BUNPC/NN22-Technical-Documents/Hardware Peripherial/ninjaNIRS Triggerbox/hardware/Rev2_KiCAD/Docs/Layout_views.pdf

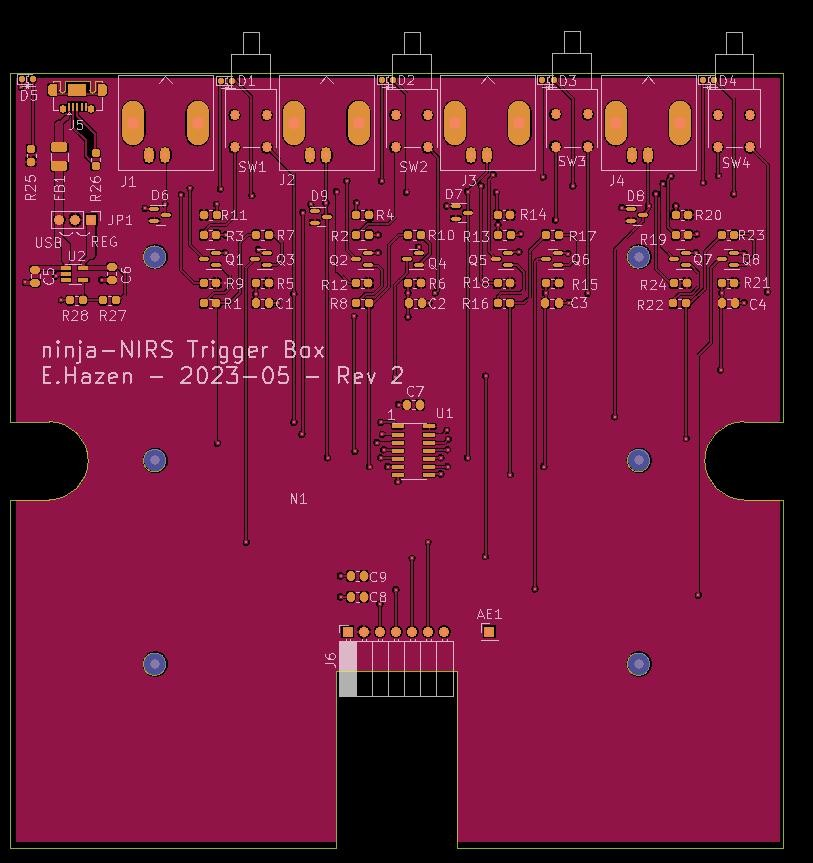
[picture p3: page 1]

Gerber view:
Front Cu, mask, silkscreen. Copper pour is “5V” power

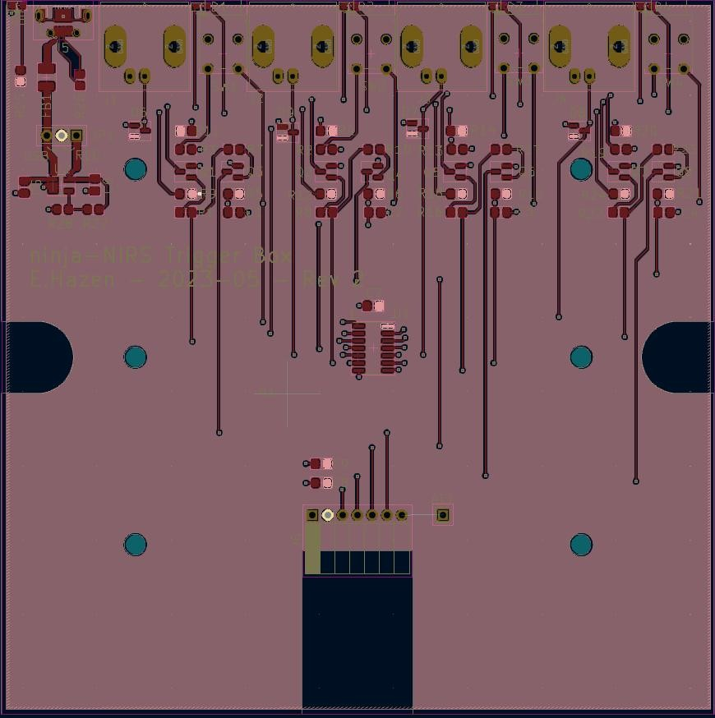
[picture p4: page 2]

5V copper pour with net highlight.

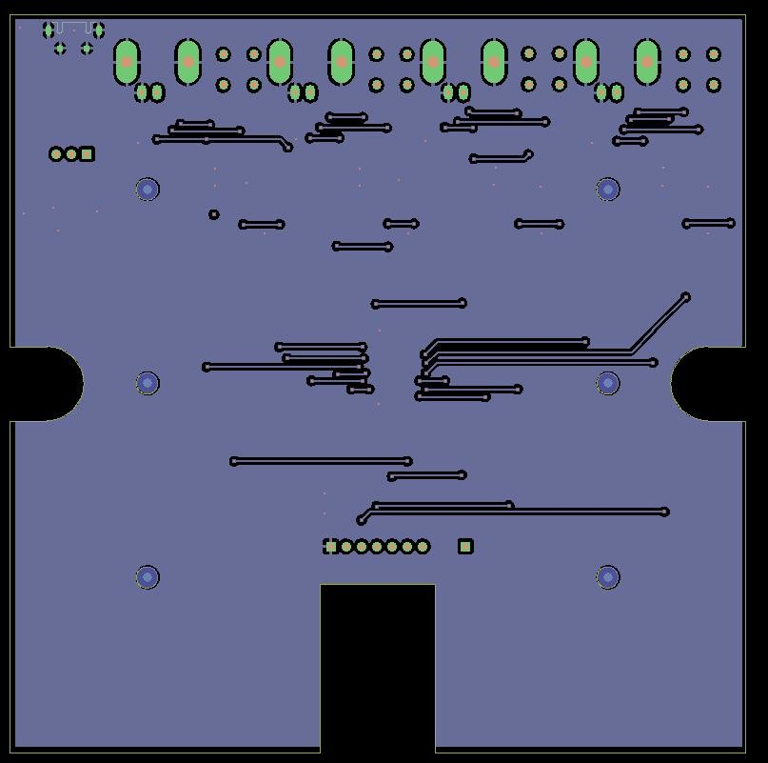
[picture p5: page 3]

Gerber view:
Back Cu, mask.
Copper area is GND

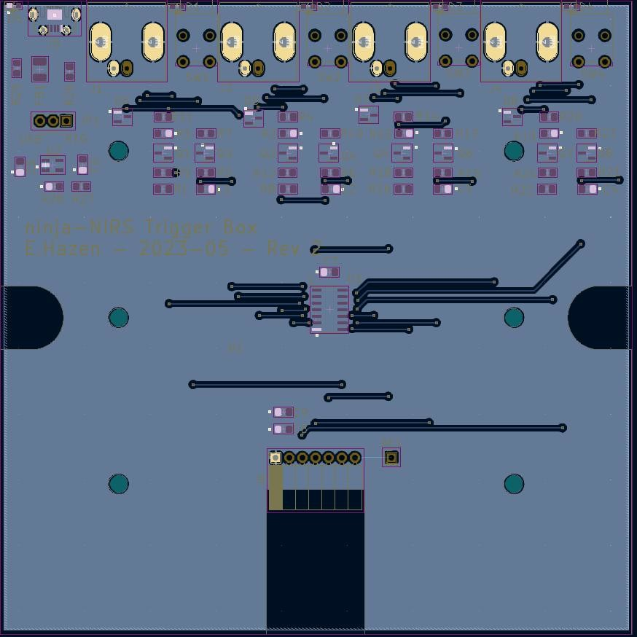
[picture p6: page 4]

Copper pour with GND highlighted

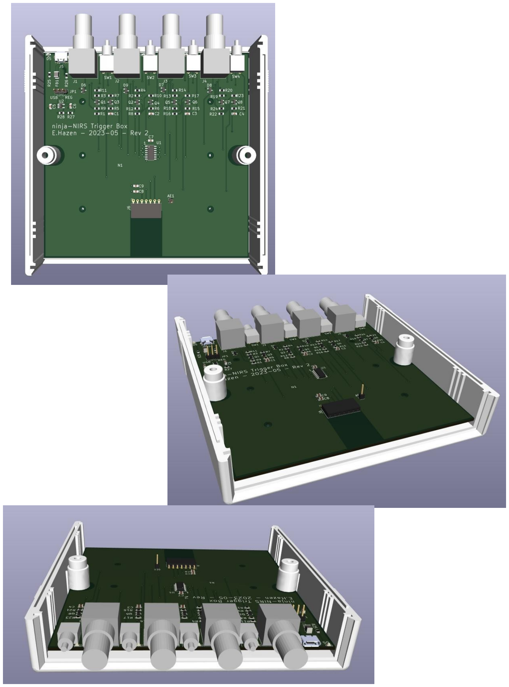
[picture p7: page 5]
