BUNPC/NN22-Technical-Documents/Hardware Main/Electronics/Source Electronics/SRC_InterfaceCard/NN22_7Lvl_ResSrcAdapter02_s00.XYRS.csv

#XYRS data for NN22_7Lvl_ResSrcAdapter02_s00.brd.
#Board Size is 2500.000000 x 1300.000000.
#
#Placement Data:
#Designator | X-Loc | Y-Loc | Rotation | Side | Type | X-Size | Y-Size | Value | Footprint | Populate | MPN
C1 | 1690.00 | 1135.00 | 180 | 1 | 1 | 340.55 | 98.43 | 100u | 2917-CAP | 1
C2 | 1960.00 | 880.00 | 270 | 1 | 1 | 169.29 | 70.87 | 22u | 1206 | 1
C3 | 2070.00 | 880.00 | 270 | 1 | 1 | 169.29 | 70.87 | 22u | 1206 | 1
C4 | 1840.00 | 790.00 | 180 | 1 | 1 | 62.99 | 19.69 | 0.1u | 0402-CAP | 1
C5 | 1675.00 | 870.00 | 270 | 1 | 1 | 62.99 | 19.69 | 47p | 0402-CAP | 1
C6 | 1600.00 | 970.00 | 180 | 1 | 1 | 169.29 | 70.87 | 22u | 1206 | 1
C7 | 1350.00 | 990.00 | 0 | 1 | 1 | 62.99 | 19.69 | 0.1u | 0402-CAP | 1
C8 | 1320.00 | 475.00 | 270 | 1 | 1 | 62.99 | 19.69 | 0.1u | 0402-CAP | 1
C9 | 1260.00 | 475.00 | 270 | 1 | 1 | 62.99 | 19.69 | 0.1u | 0402-CAP | 1
C10 | 1240.00 | 190.00 | 270 | 1 | 1 | 169.29 | 70.87 | 22u | 1206 | 1
C11 | 1240.00 | 1110.00 | 90 | 1 | 1 | 169.29 | 70.87 | 22u | 1206 | 1
D1 | 170.00 | 950.00 | 0 | 2 | 1 | 78.74 | 27.56 | SBR1A20T5 | SOD523 | 1
D2 | 335.00 | 850.00 | 0 | 2 | 1 | 78.74 | 27.56 | SBR1A20T5 | SOD523 | 1
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
