BUNPC/NN22-Technical-Documents/Hardware Peripherial/ninjaNIRS Triggerbox/hardware/Rev1a_Eagle/81kcTXVxWdL._AC_SL1500_.jpg

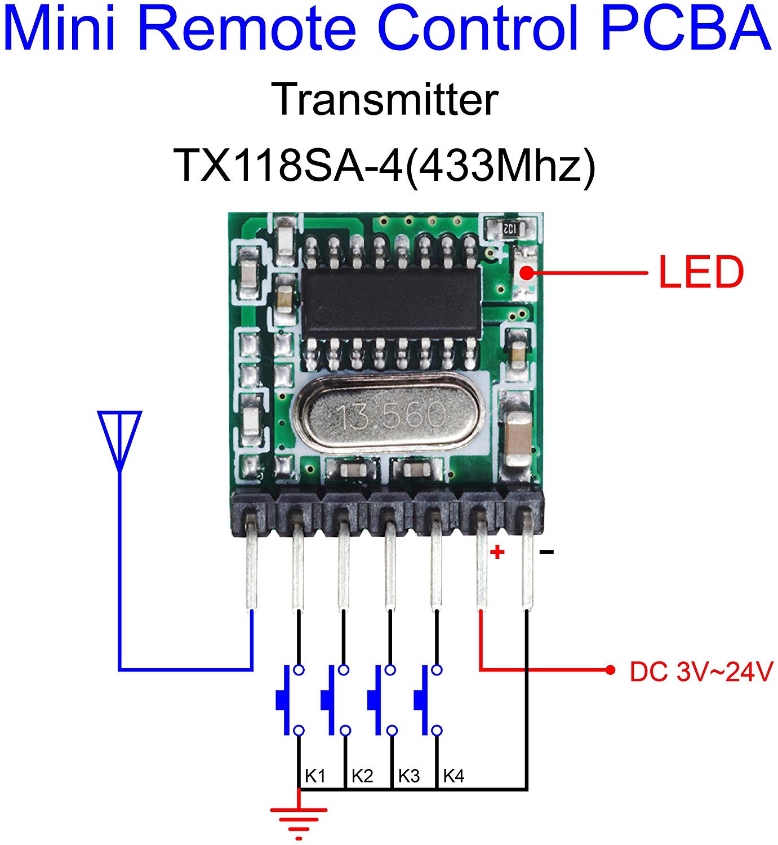
Hardware Peripherial/ninjaNIRS Triggerbox/hardware/Rev1a_Eagle/81kcTXVxWdL._AC_SL1500_.jpg
