BUNPC/NN22-Technical-Documents/Hardware Main/Electronics/Detector Electronics/Det_InterfaceCard/NN22_RPi_DetAdapter02_s00_BOM.xlsx

Designator | Value | Footprint | Populate | MPN | Manufacturer
C1 | 330p | 0402-CAP | 1 | GRM1555C1H331JA01D | Murata
C10 | 0.1u | 0402-CAP | 1 | GRM155R71H104KE14D | Murata
C100 | 0.1u | 0402-CAP | 1 | GRM155R71H104KE14D | Murata
C101 | 0.1u | 0402-CAP | 1 | GRM155R71H104KE14D | Murata
C102 | 0.1u | 0402-CAP | 1 | GRM155R71H104KE14D | Murata
C103 | 0.1u | 0402-CAP | 1 | GRM155R71H104KE14D | Murata
C104 | 10u | 0603-CAP | 1 | GRM188R6YA106MA73D | Murata
C105 | 4.7u | 0402-CAP | 1 | CL05A475MP5NRNC | Samsung
C106 | 10u | 0603-CAP | 1 | GRM188R6YA106MA73D | Murata
C107 | 4.7u | 0402-CAP | 1 | CL05A475MP5NRNC | Samsung
C108 | 10u | 0603-CAP | 1 | GRM188R6YA106MA73D | Murata
C109 | 10u | 0603-CAP | 1 | GRM188R6YA106MA73D | Murata
C11 | 330p | 0402-CAP | 1 | GRM1555C1H331JA01D | Murata
C110 | 33n | 0402-CAP | 1 | GCM155R71E333KA55D | Murata
C111 | 4.7u | 0402-CAP | 1 | CL05A475MP5NRNC | Samsung
C112 | 4.7u | 0402-CAP | 1 | CL05A475MP5NRNC | Samsung
C113 | 4.7u | 0402-CAP | 1 | CL05A475MP5NRNC | Samsung
C12 | 1u | 0402-CAP | 1 | CL05A105KP5NNNC | Samsung
C13 | 0.1u | 0402-CAP | 1 | GRM155R71H104KE14D | Murata
C14 | 1u | 0402-CAP | 1 | CL05A105KP5NNNC | Samsung
C15 | 1n | 0402-CAP | 1 | GRM1555C1H102JA01D | Murata
C16 | 1n | 0402-CAP | 1 | GRM1555C1H102JA01D | Murata
C17 | 1n | 0402-CAP | 1 | GRM1555C1H102JA01D | Murata
C18 | 330p | 0402-CAP | 1 | GRM1555C1H331JA01D | Murata
C19 | 0.1u | 0402-CAP | 1 | GRM155R71H104KE14D | Murata
C2 | 1n | 0402-CAP | 1 | GRM1555C1H102JA01D | Murata
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
TP8 | TESTPOINT_ROUND | TESTPAD_ROUND | 0
TP9 | TESTPOINT_ROUND | TESTPAD_ROUND | 0
U1 | AD7380 | LFCSP16 | 1 | AD7380BCPZ-RL7 | Analog Devices
U10 | RP2040 | QFN-56_EP | 1 | SC0914(7) | Raspberry Pi
U11 | MCP1755_DFN | DFN8_2X3MM | 1 | MCP1755-3302E/MC | Microchip
U12 | MCP1755_DFN | DFN8_2X3MM | 1 | MCP1755-3302E/MC | Microchip
U13 | ADP7142_WSON | WSON6 | 1 | ADP7142ACPZN5.0-R7 | Analog Devices
U14 | ADP7182_WSON | WSON6 | 1 | ADP7182ACPZN-R7 | Analog Devices
U15 | ADP7182_WSON | WSON6 | 1 | ADP7182ACPZN-R7 | Analog Devices
U2 | ADA4940-2 | LFCSP24 | 1 | ADA4940-2ACPZ-R7 | Analog Devices
U3 | AD7380 | LFCSP16 | 1 | AD7380BCPZ-RL7 | Analog Devices
U4 | ADA4940-2 | LFCSP24 | 1 | ADA4940-2ACPZ-R7 | Analog Devices
U5 | AD7380 | LFCSP16 | 1 | AD7380BCPZ-RL7 | Analog Devices
U6 | ADA4940-2 | LFCSP24 | 1 | ADA4940-2ACPZ-R7 | Analog Devices
U7 | AD7380 | LFCSP16 | 1 | AD7380BCPZ-RL7 | Analog Devices
U8 | ADA4940-2 | LFCSP24 | 1 | ADA4940-2ACPZ-R7 | Analog Devices
U9 | W25Q_USON | USON8L-2X3MM | 1 | W25Q16JVUXIQ TR | Winbond
X1 | CRYSTAL-3.2-2.5 | CRYSTAL-3.2-2.5 | 1 | 403I35D12M00000 | CTS Components
