BUNPC/NN22-Technical-Documents/Hardware Peripherial/ninjaNIRS Triggerbox/hardware/Rev2_KiCAD/3D/1598B Top.stp

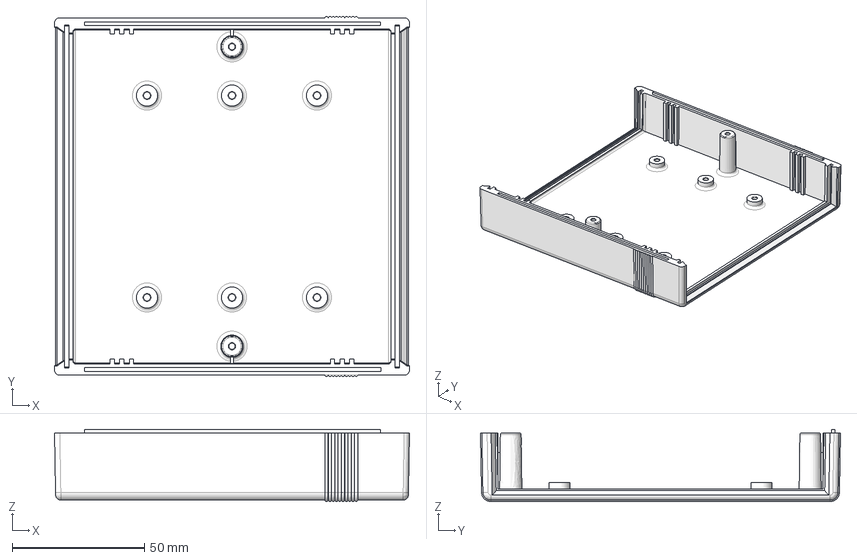
[picture p27: CAD file, 2024-05-28]
Hardware Peripherial/ninjaNIRS Triggerbox/hardware/Rev2_KiCAD/3D/1598B Top.stp
134.3 x 136.2 x 27.2 mm
