BUNPC/NN22-Technical-Documents/Hardware Peripherial/ninjaNIRS Triggerbox/hardware/Rev2_KiCAD/panel/panel.dxf

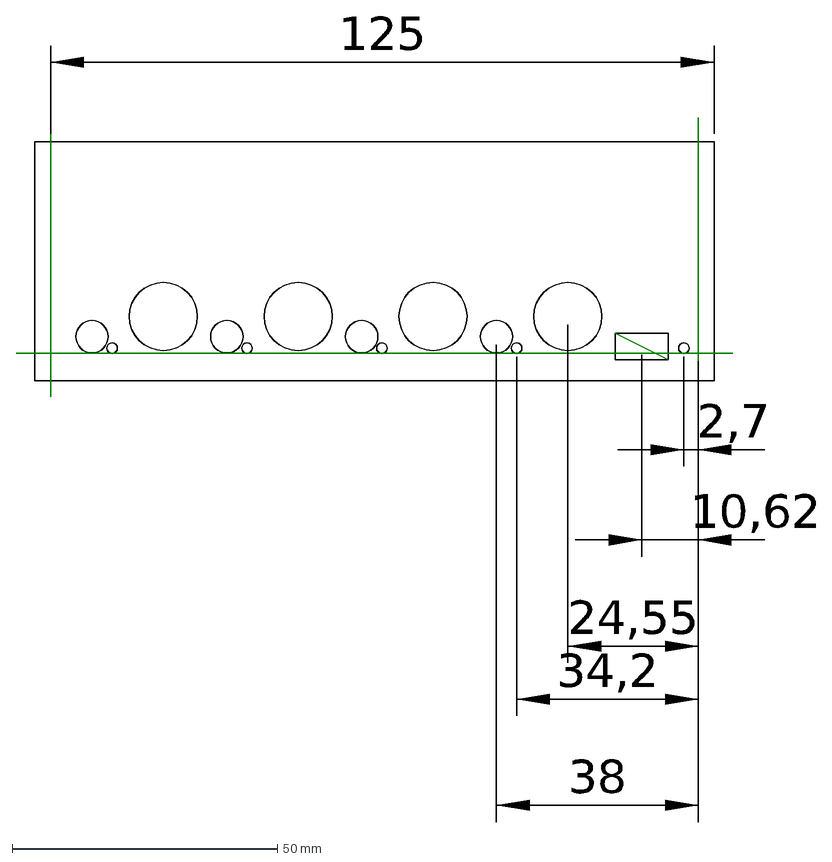
[picture p28: CAD file, 2024-05-28]
Hardware Peripherial/ninjaNIRS Triggerbox/hardware/Rev2_KiCAD/panel/panel.dxf
125
2,7
10,62
24,55
34,2
38
