BUNPC/NN22-Technical-Documents/Hardware Peripherial/ninjaNIRS Triggerbox/hardware/Rev2_KiCAD/trigger-board/Hammond_1598B.dxf

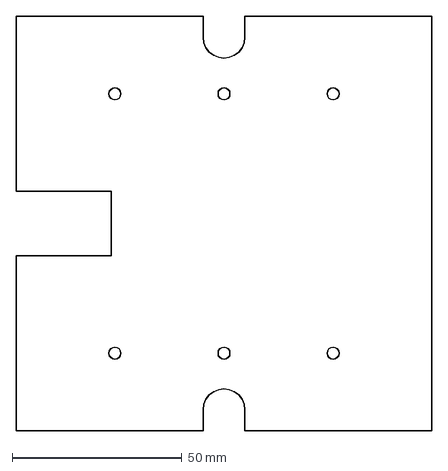
[picture p29: CAD file, 2024-05-28]
Hardware Peripherial/ninjaNIRS Triggerbox/hardware/Rev2_KiCAD/trigger-board/Hammond_1598B.dxf
122.3 x 122.0 mm
