BUNPC/NN22-Technical-Documents/IMU-bundle/ninjanirs-imu-main/KiCAD/(Delete) imu-board/models/ATTINY10-MAHR.step

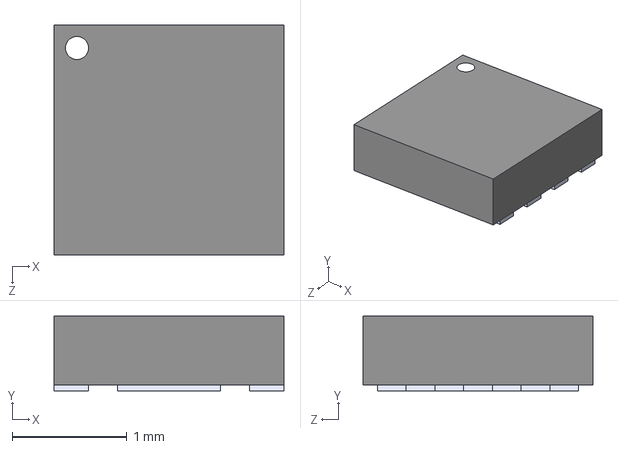
[picture p30: CAD file, 2024-05-28]
IMU-bundle/ninjanirs-imu-main/KiCAD/(Delete) imu-board/models/ATTINY10-MAHR.step
2.00 x 0.65 x 2.00 mm
