BUNPC/NN22-Technical-Documents/IMU-bundle/ninjanirs-imu-main/KiCAD/(Delete) imu-splitter/3D/1551TGY.stp

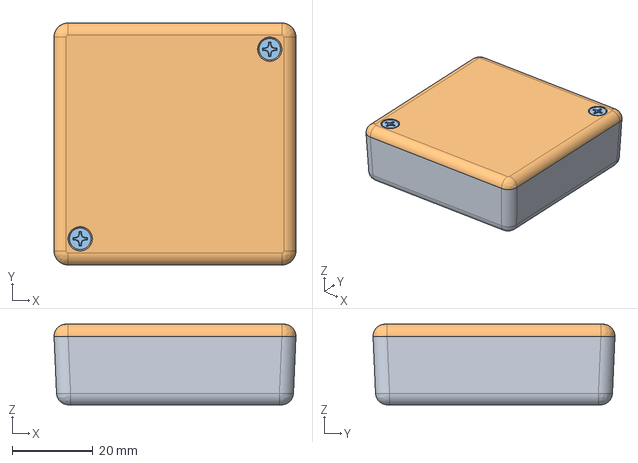
[picture p31: CAD file, 2024-05-28]
IMU-bundle/ninjanirs-imu-main/KiCAD/(Delete) imu-splitter/3D/1551TGY.stp
60.0 x 60.0 x 20.0 mm
1551T Box
1551T Lid
