BUNPC/NN22-Technical-Documents/Hardware Main/Electronics/IMU Electronics/IMU_Splitter/3D/A-2004-3-4-Group.step

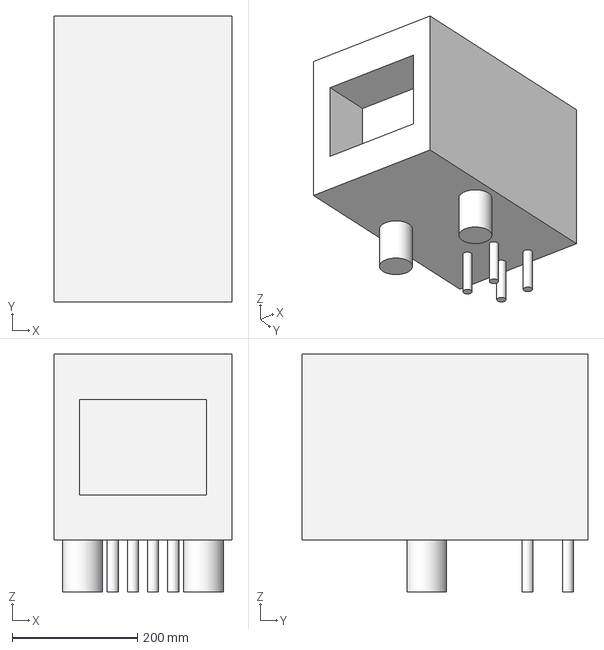
[picture p32: CAD file, 2024-05-28]
Hardware Main/Electronics/IMU Electronics/IMU_Splitter/3D/A-2004-3-4-Group.step
284.5 x 457.2 x 379.7 mm
