BUNPC/NN22-Technical-Documents/Hardware Peripherial/ninjaNIRS Triggerbox/hardware/Rev2_KiCAD/3D/PCB_BNC.stl

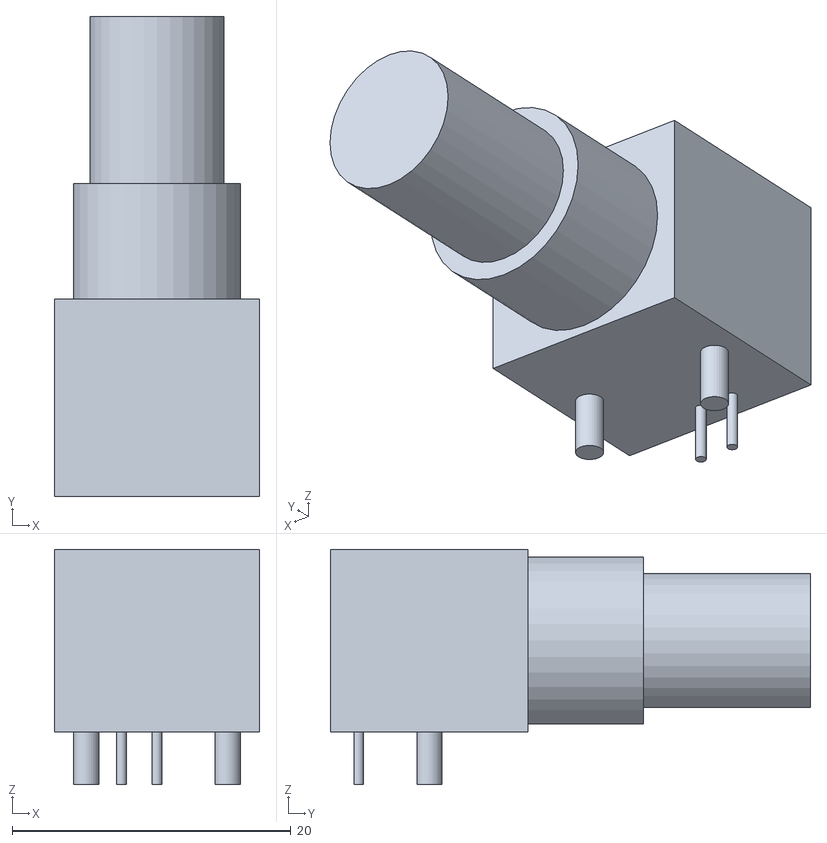
[picture p34: CAD file, 2024-05-28]
Hardware Peripherial/ninjaNIRS Triggerbox/hardware/Rev2_KiCAD/3D/PCB_BNC.stl
14.8 x 34.5 x 16.9
