BUNPC/NN22-Technical-Documents/IMU-bundle/ninjanirs-imu-main/KiCAD/(Delete) imu-splitter/3D/1551T.dxf

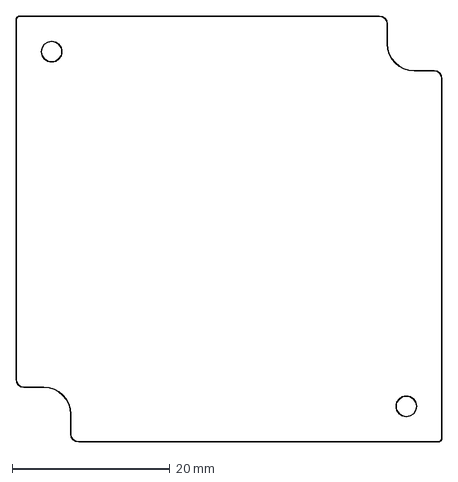
[picture p35: CAD file, 2024-05-28]
IMU-bundle/ninjanirs-imu-main/KiCAD/(Delete) imu-splitter/3D/1551T.dxf
54.0 x 54.0 mm
