BUNPC/NN22-Technical-Documents/Hardware Peripherial/ninjaNIRS Triggerbox/hardware/Rev2_KiCAD/3D/1598B End Plate.stp

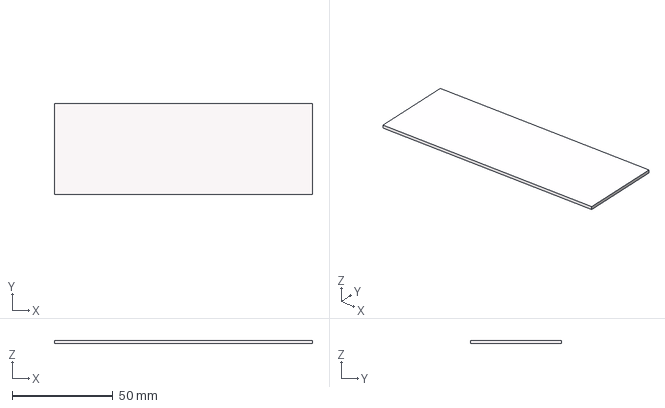
[picture p36: CAD file, 2024-05-28]
Hardware Peripherial/ninjaNIRS Triggerbox/hardware/Rev2_KiCAD/3D/1598B End Plate.stp
128.0 x 45.0 x 1.65 mm
