BUNPC/NN22-Technical-Documents/Hardware Main/Electronics/Source Electronics/SRC_InterfaceCard/NN22_7Lvl_ResSrcAdapter02_s00.pdf

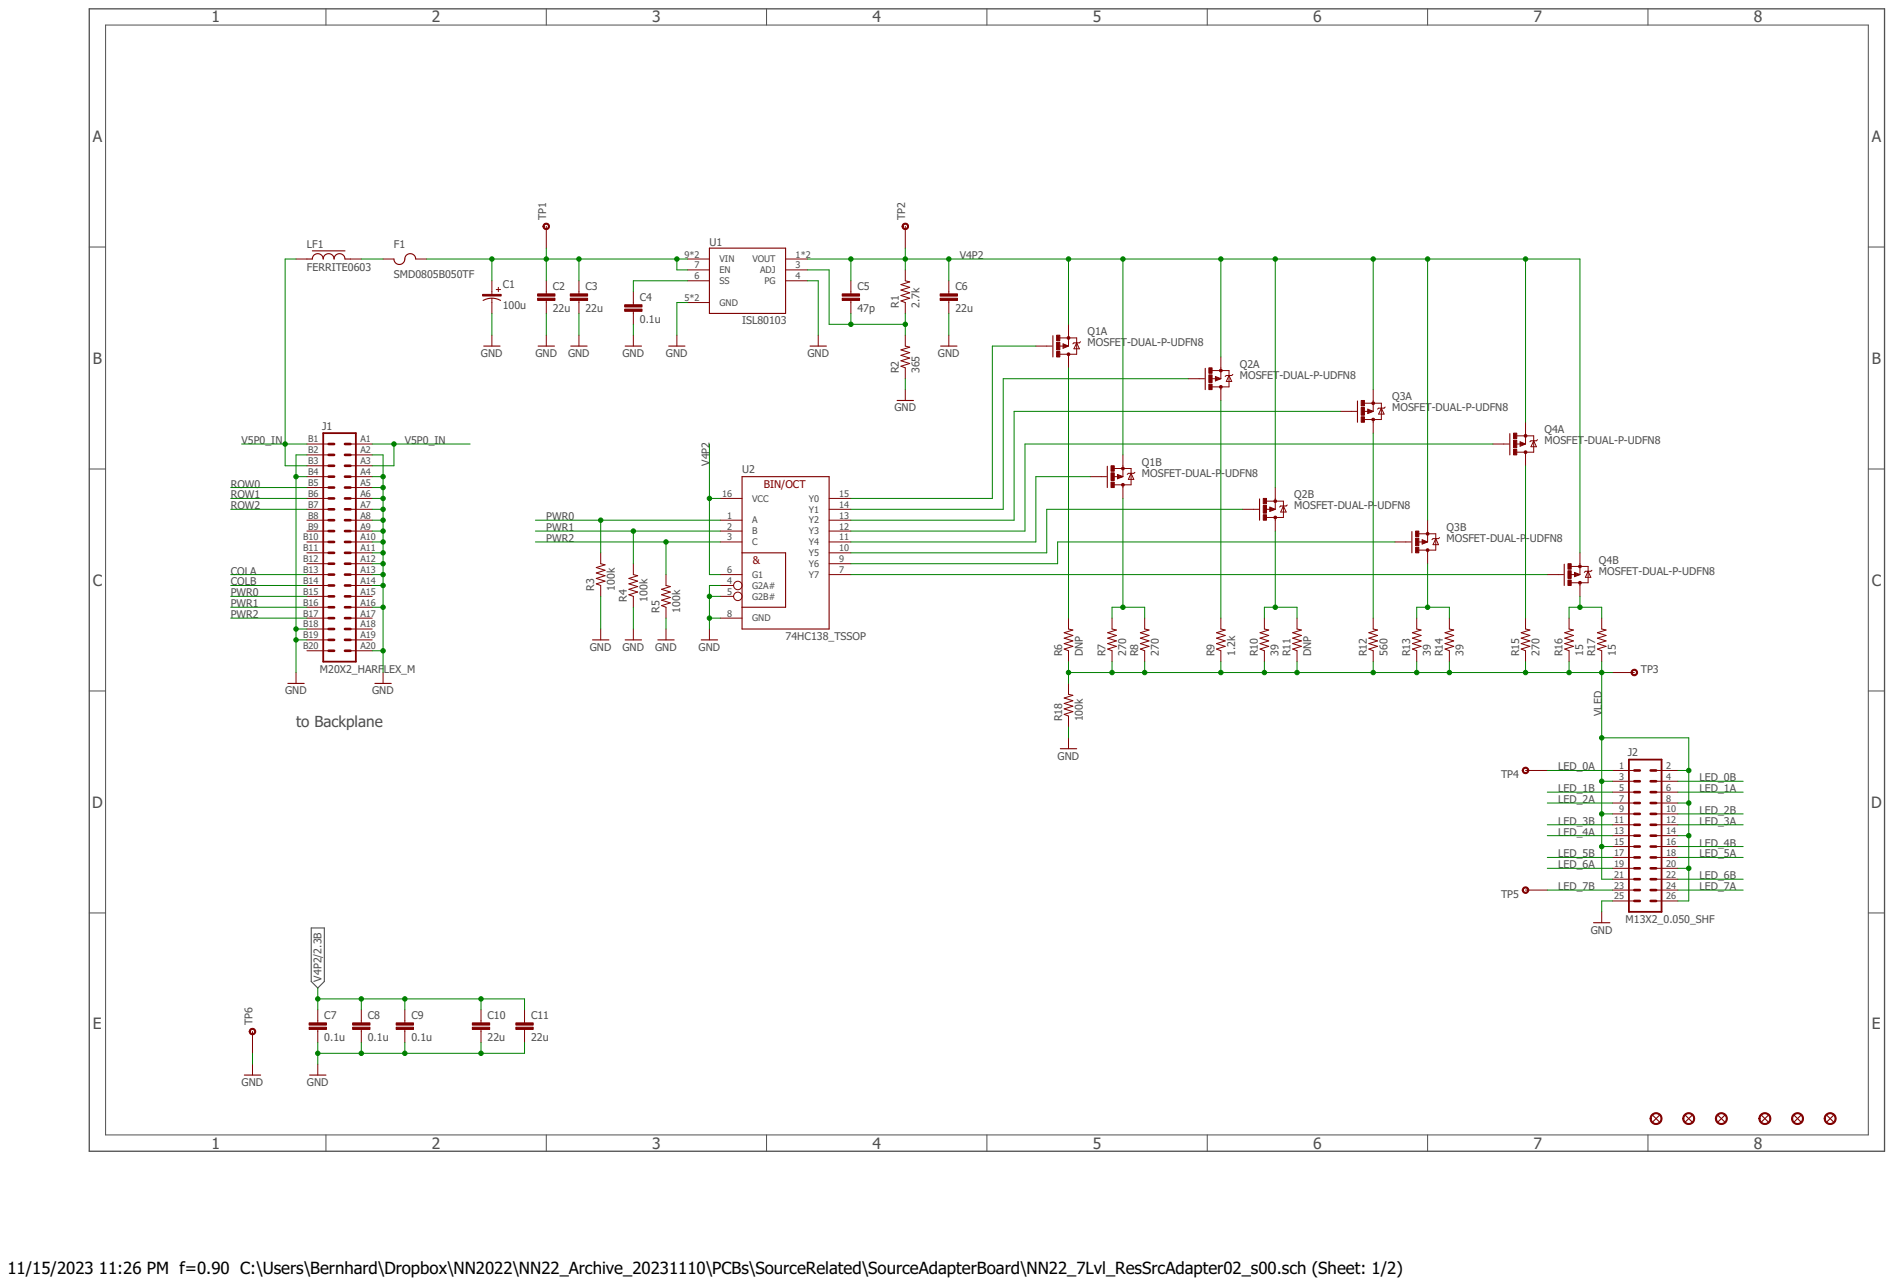
[picture p96: page 1]

11/15/2023 11:26 PM f=0.90 C:\Users\Bernhard\Dropbox\NN2022\NN22_Archive_20231110\PCBs\SourceRelated\SourceAdapterBoard\NN22_7Lvl_ResSrcAdapter02_s00.sch (Sheet: 1/2)

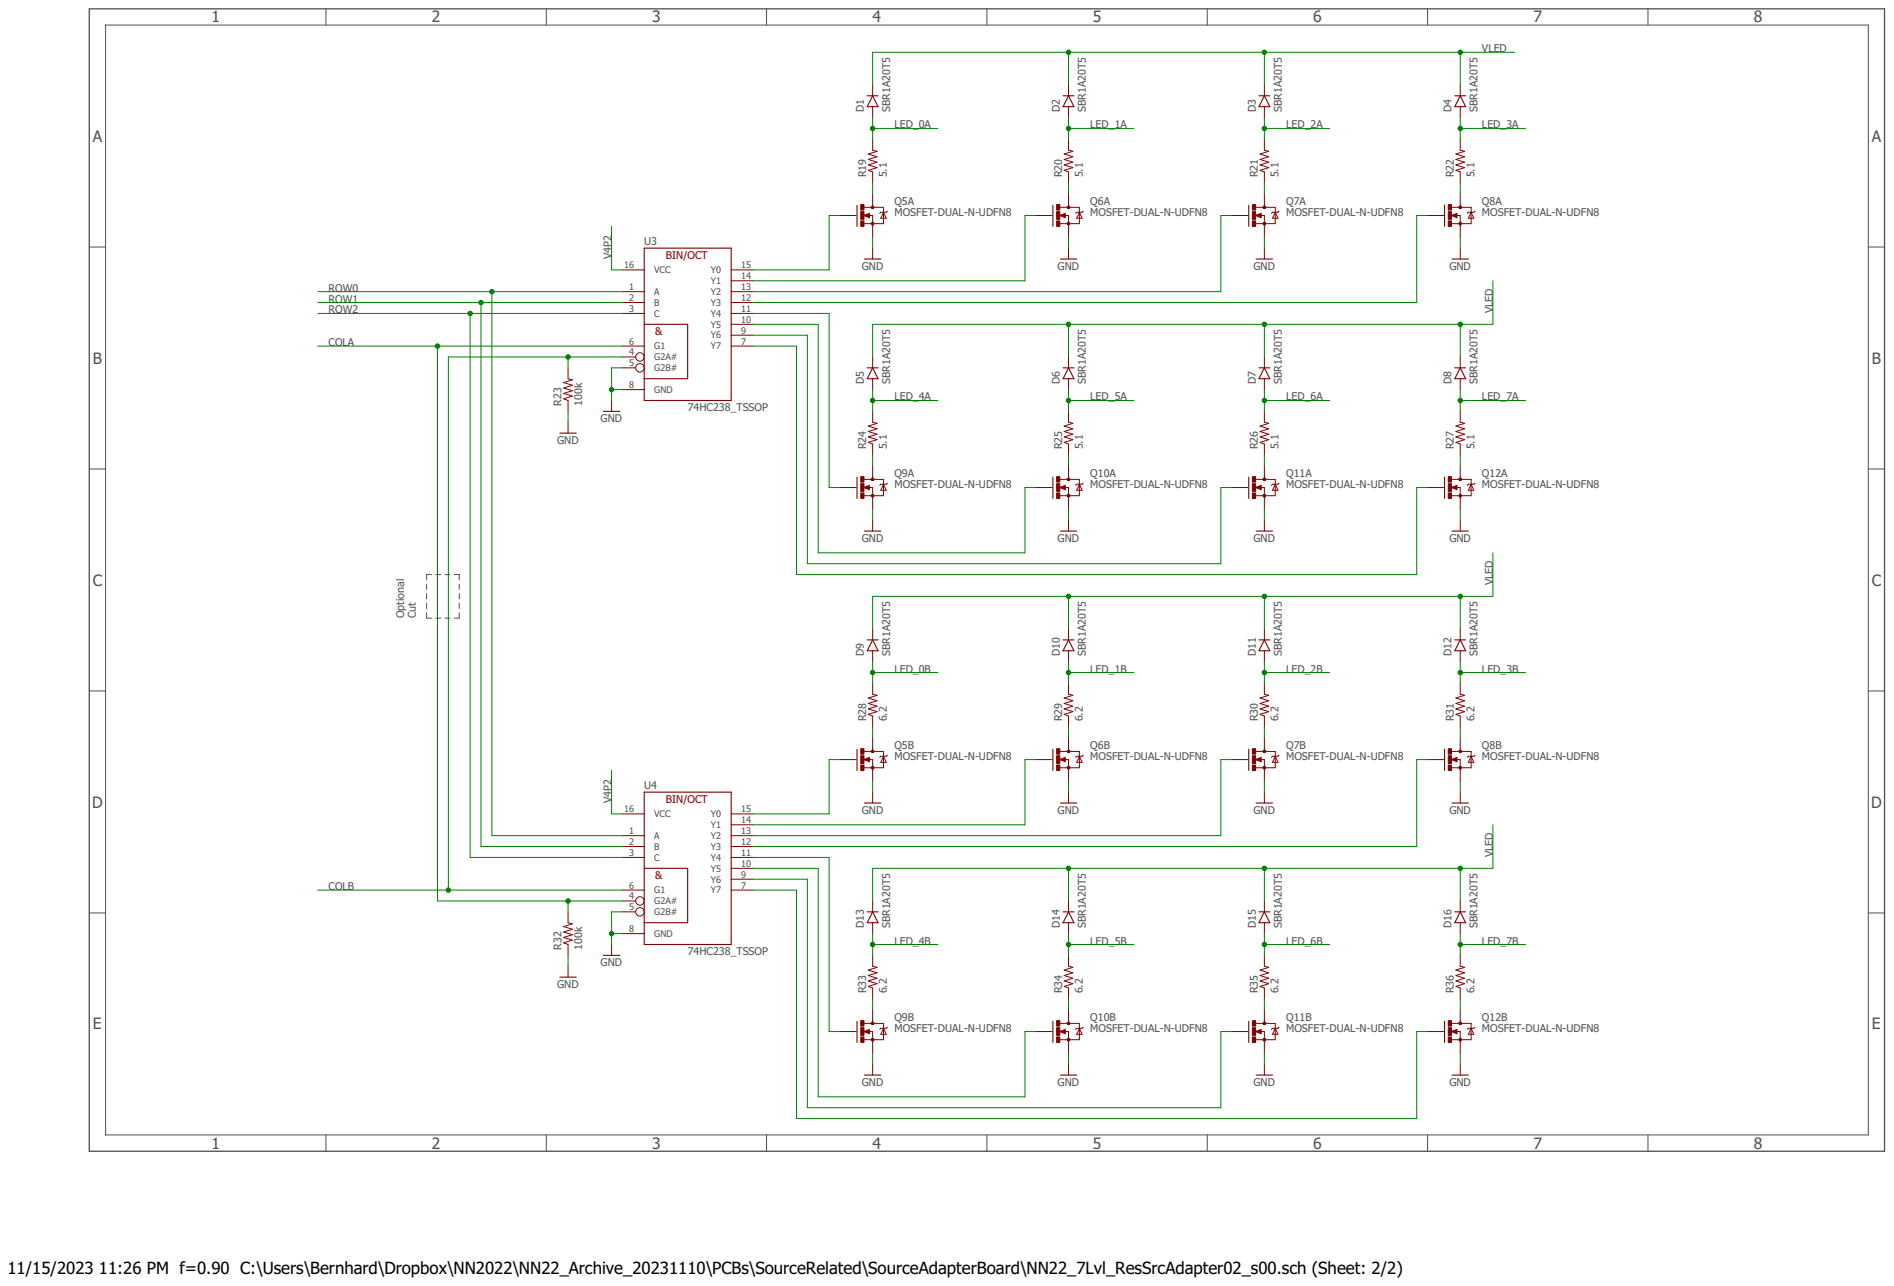
[picture p97: page 2]

VLED

11/15/2023 11:26 PM f=0.90 C:\Users\Bernhard\Dropbox\NN2022\NN22_Archive_20231110\PCBs\SourceRelated\SourceAdapterBoard\NN22_7Lvl_ResSrcAdapter02_s00.sch (Sheet: 2/2)
