BUNPC/NN22-Technical-Documents/Hardware Main/Electronics/Detector Electronics/DET_Optode/flex-VEMD/flex-VEMD.pdf

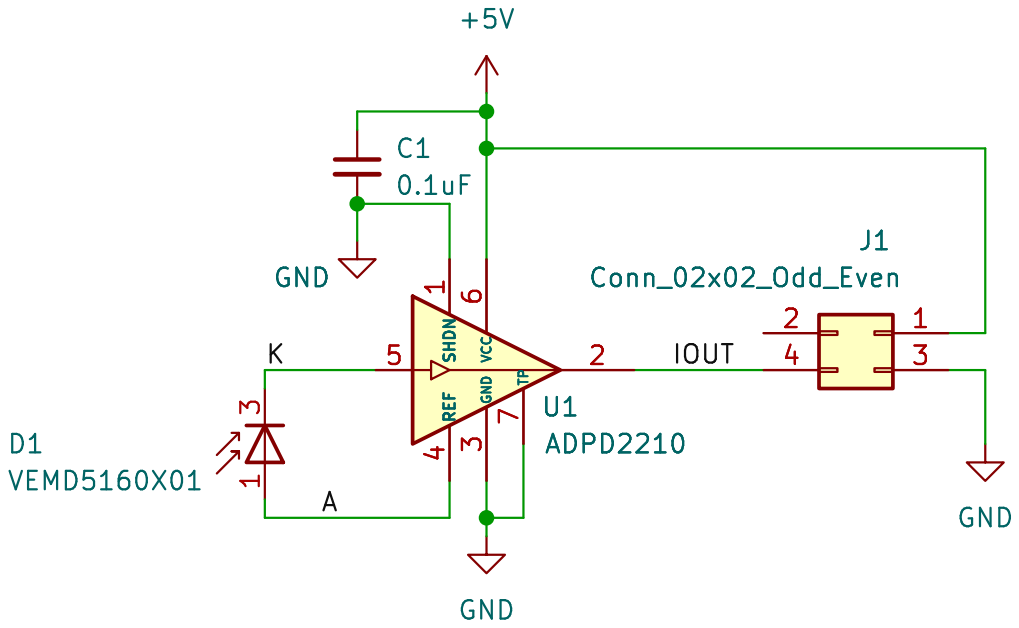
[picture p98: page 1]

Id: 1/1 Title: File: flex-VEMD.kicad_sch Sheet: / GND GND SHDN 1
