BUNPC/NN22-Technical-Documents/Hardware Peripherial/ninjaNIRS Triggerbox/hardware/Rev2_KiCAD/trigger-board/trigger-board.pdf

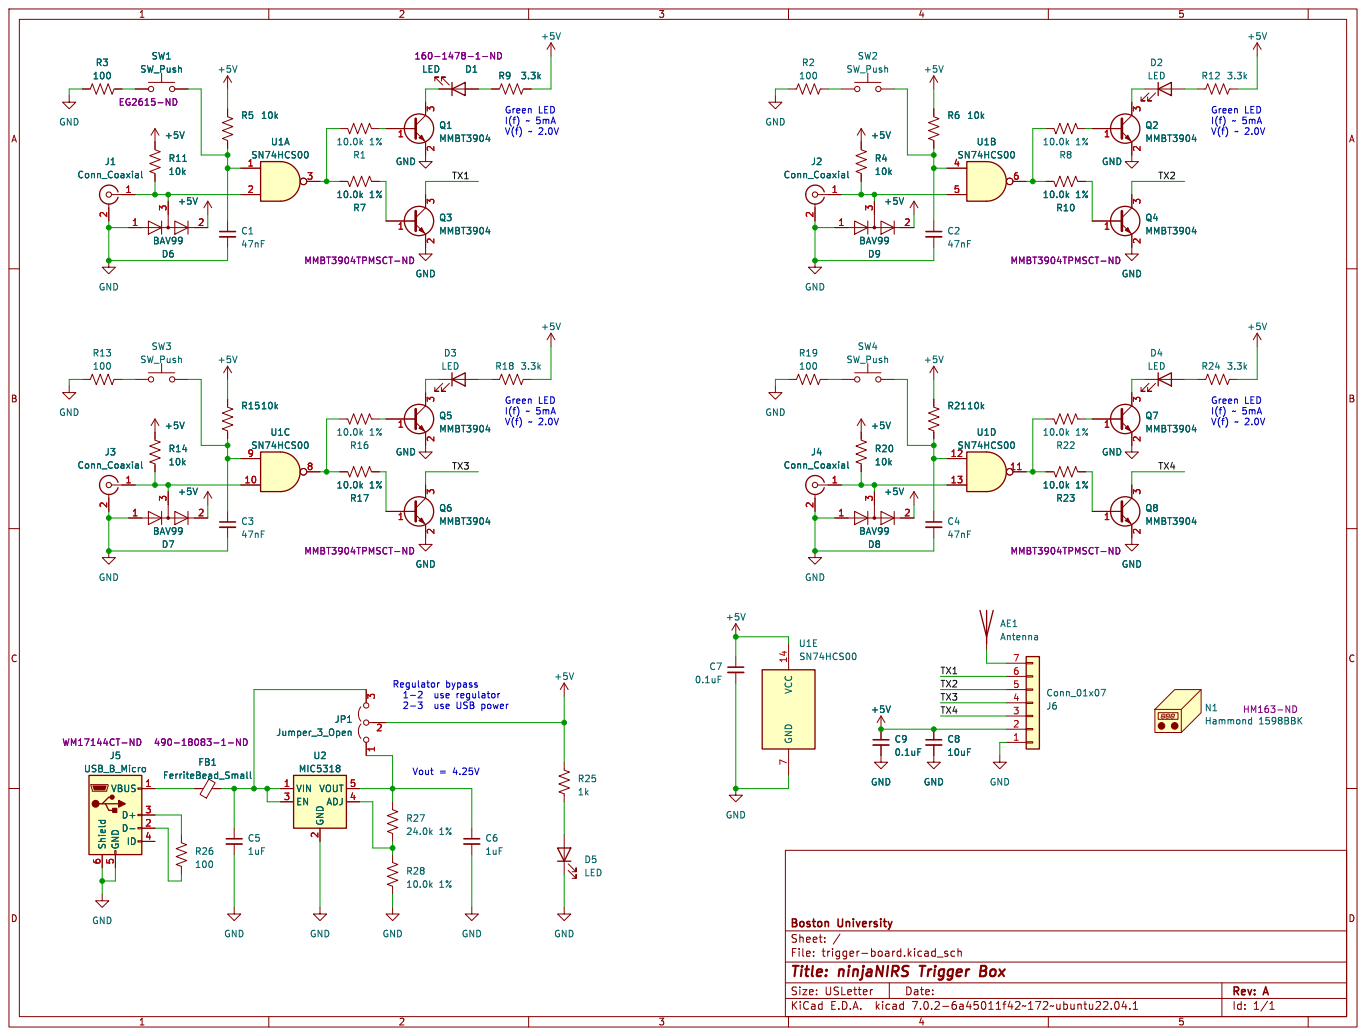
[picture p99: page 1]

2 VIN 1 EN 3 ADJ 4 VOUT 5 R15 10k Q5 MMBT3904 1

File: trigger-board.kicad_sch Sheet: / Boston University GND

2 VIN 1 EN 3 ADJ 4 VOUT 5 U2 MIC5318 R26

Id: 1/1 Title: ninjaNIRS Trigger Box
