BUNPC/NN22-Technical-Documents/Hardware Main/Electronics/Detector Electronics/DET_Backplane/DetBackplane_SixLayer/DetBackplane01.pdf

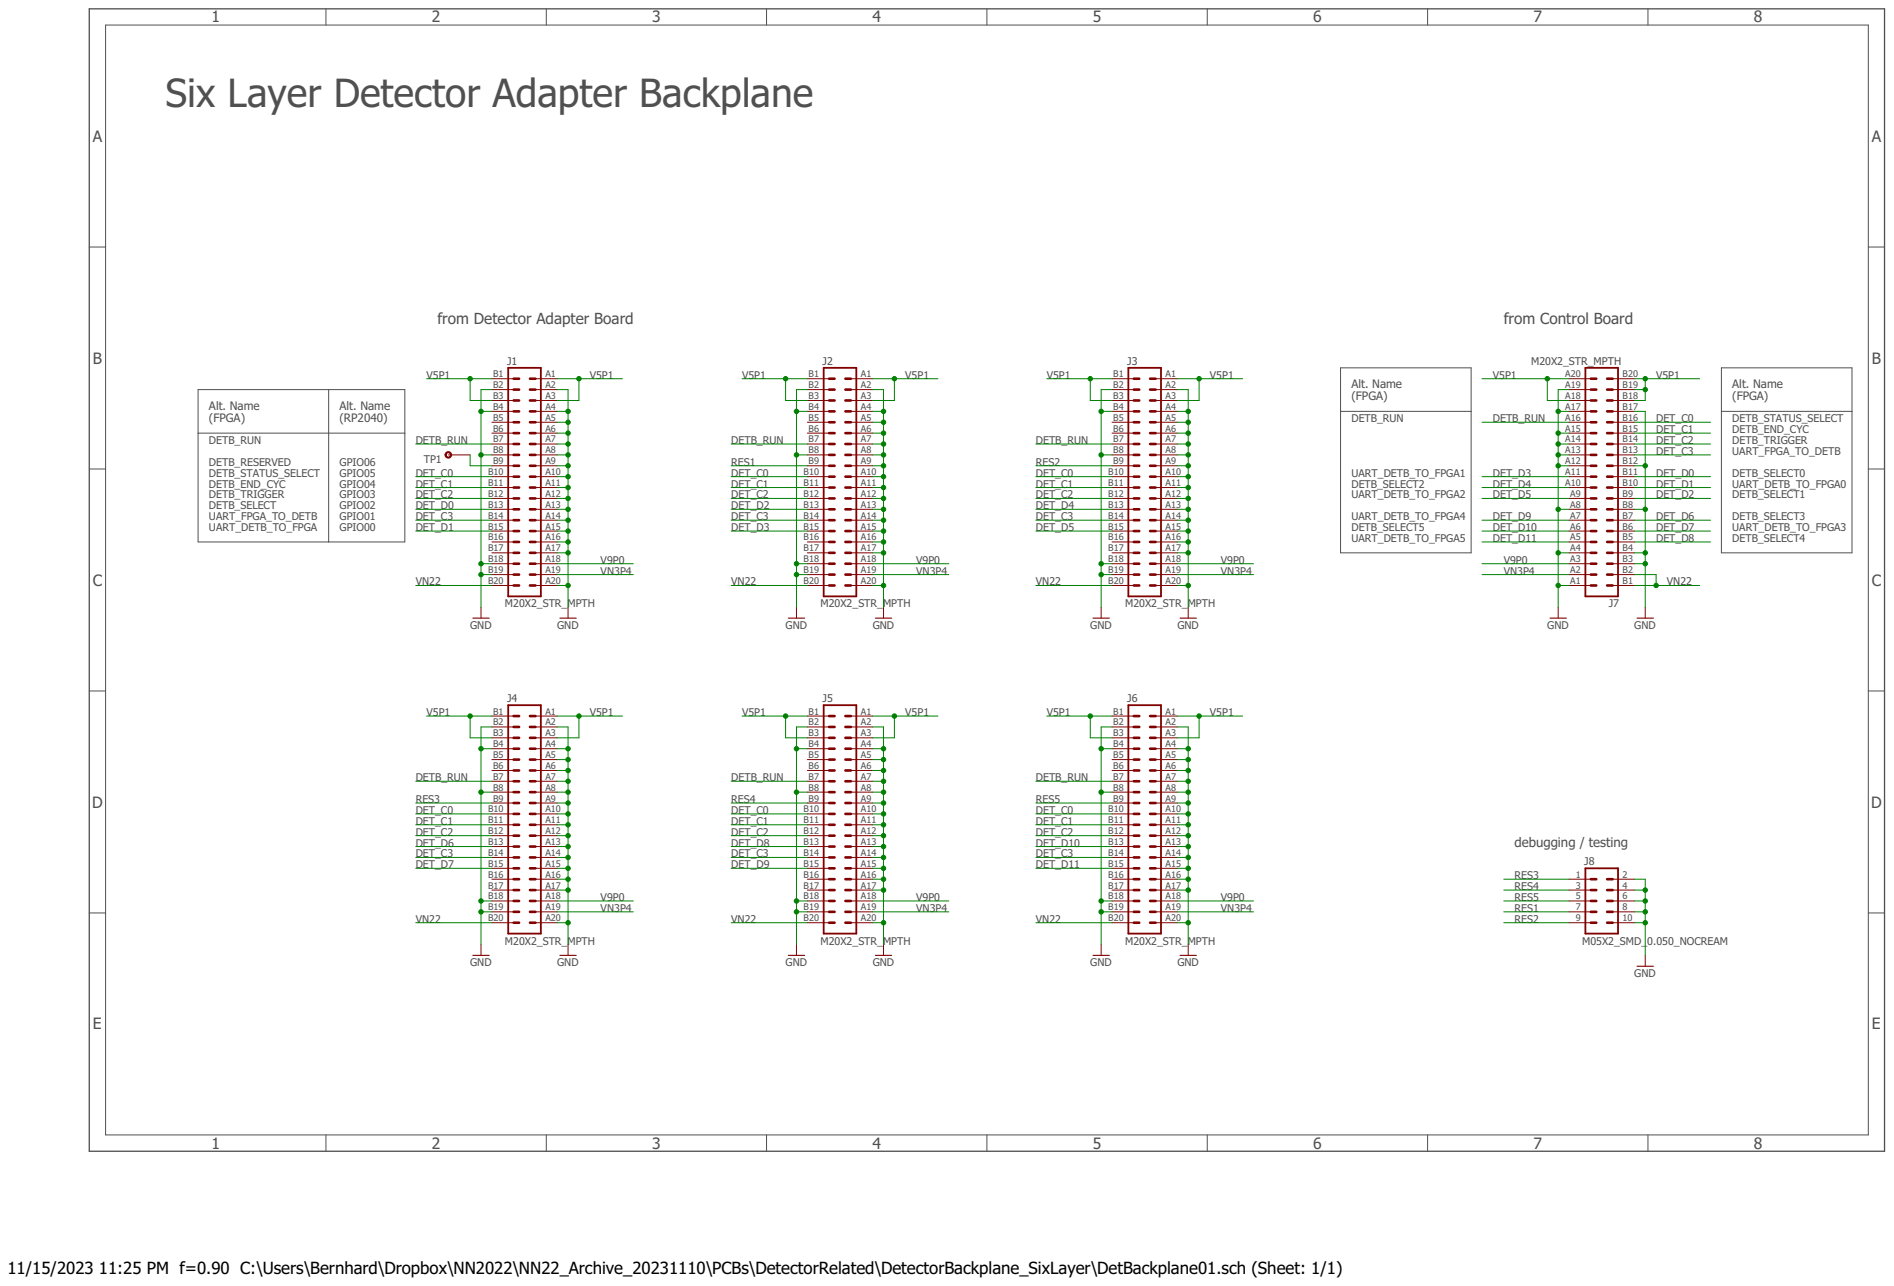
[picture p100: page 1]

Six Layer Detector Adapter Backplane

Alt. Name (FPGA) | Alt. Name (RP2040)

DETB_RUN DETB_RESERVED DETB_STATUS_SELECT DETB_END_CYC DETB_TRIGGER DETB_SELECT UART_FPGA_TO_DETB UART_DETB_TO_FPGA | GPIO06 GPIO05 GPIO04 GPIO03 GPIO02 GPIO01 GPIO00

11/15/2023 11:25 PM f=0.90 C:\Users\Bernhard\Dropbox\NN2022\NN22_Archive_20231110\PCBs\DetectorRelated\DetectorBackplane_SixLayer\DetBackplane01.sch (Sheet: 1/1)
