BUNPC/NN22-Technical-Documents/Hardware Main/Electronics/Source Electronics/SRC_Backplane/SrcBackplane_SingleLayer/SrcBackplaneSingleLayer00_01.pdf

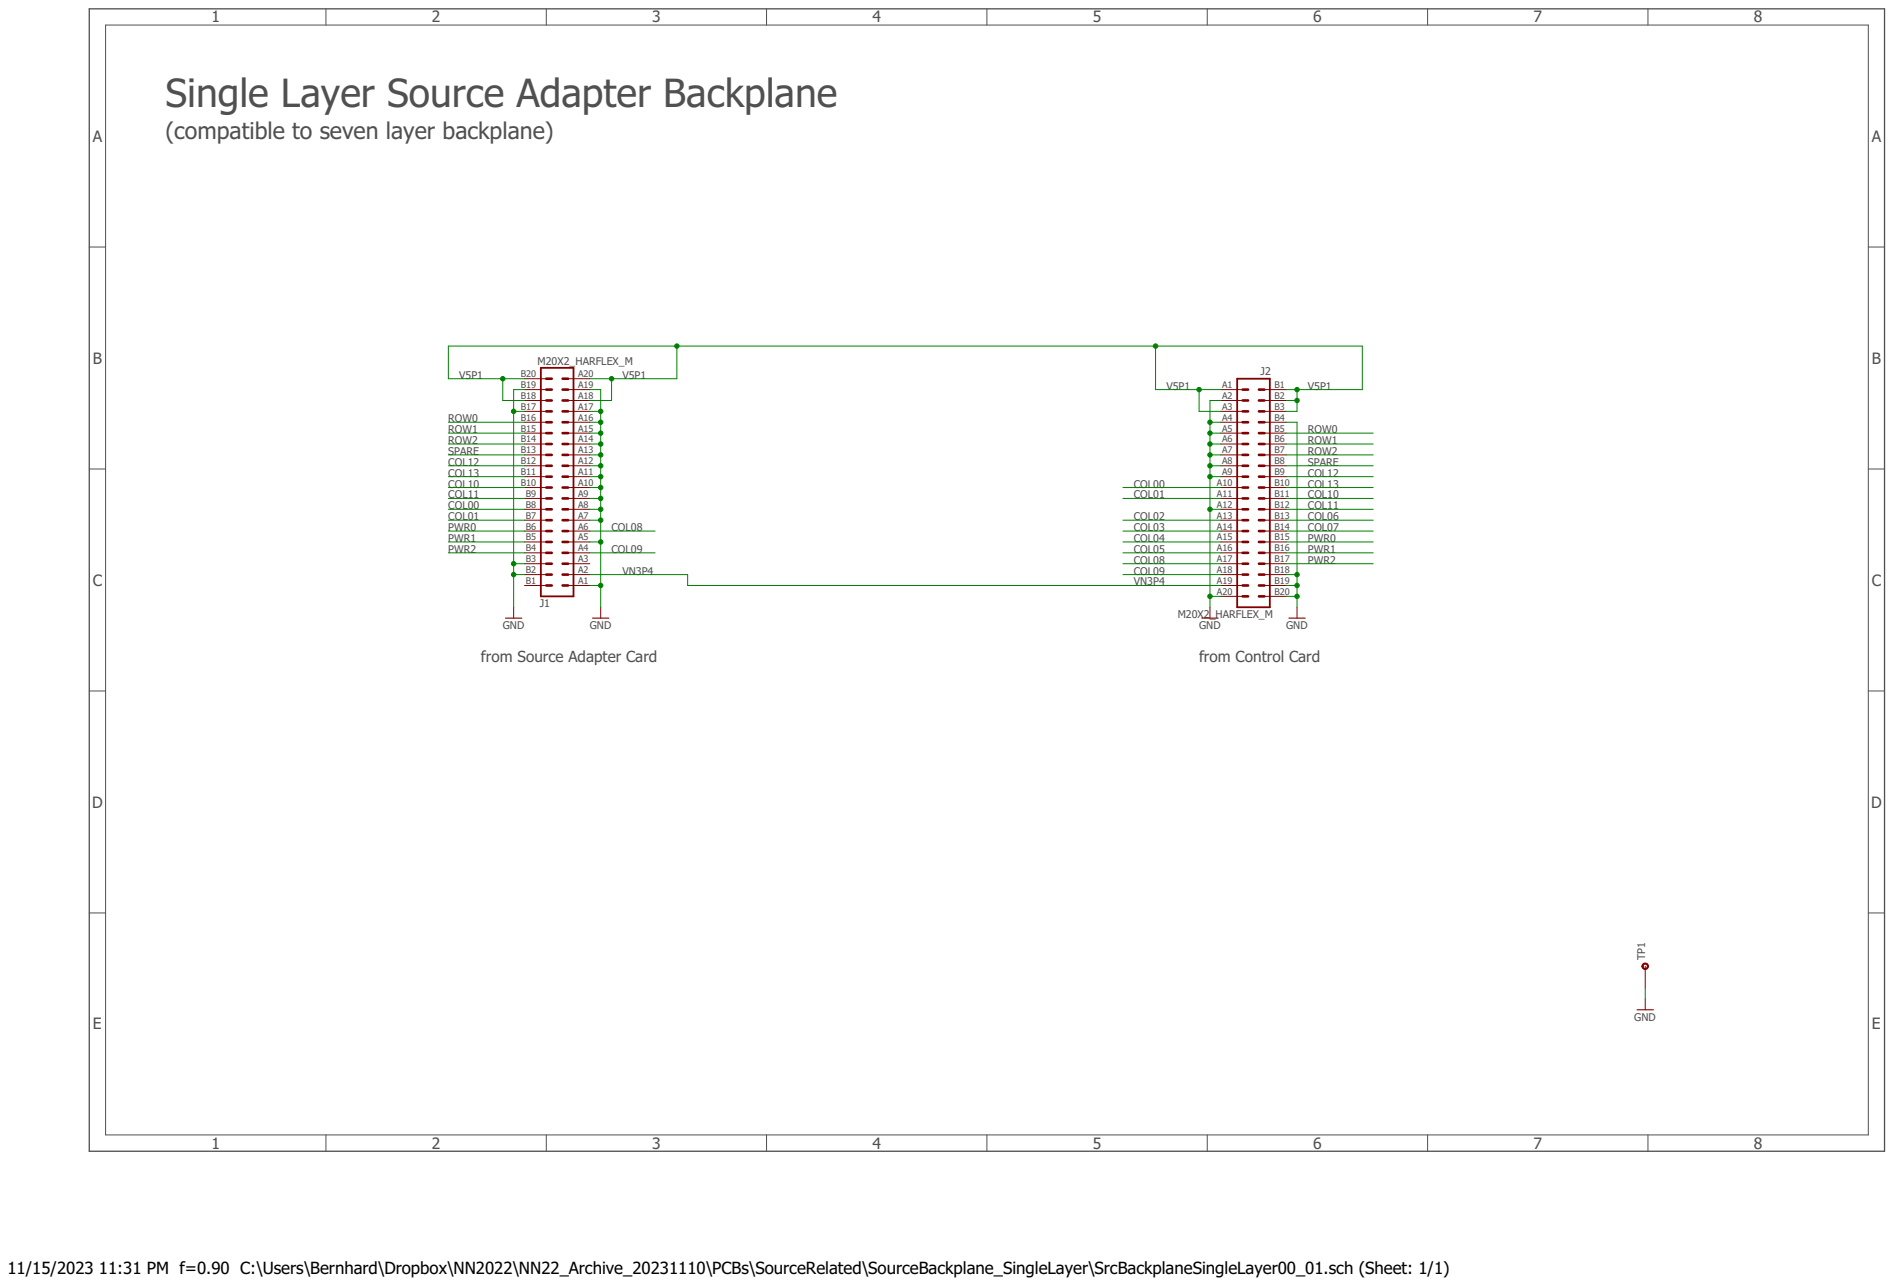
[picture p101: page 1]

Single Layer Source Adapter Backplane

(compatible to seven layer backplane)

11/15/2023 11:31 PM f=0.90 C:\Users\Bernhard\Dropbox\NN2022\NN22_Archive_20231110\PCBs\SourceRelated\SourceBackplane_SingleLayer\SrcBackplaneSingleLayer00_01.sch (Sheet: 1/1)
