BUNPC/NN22-Technical-Documents/Hardware Main/Electronics/Source Electronics/SRC_Backplane/SrcBackplane_SevenLayer/SrcBackplane01_7slots.pdf

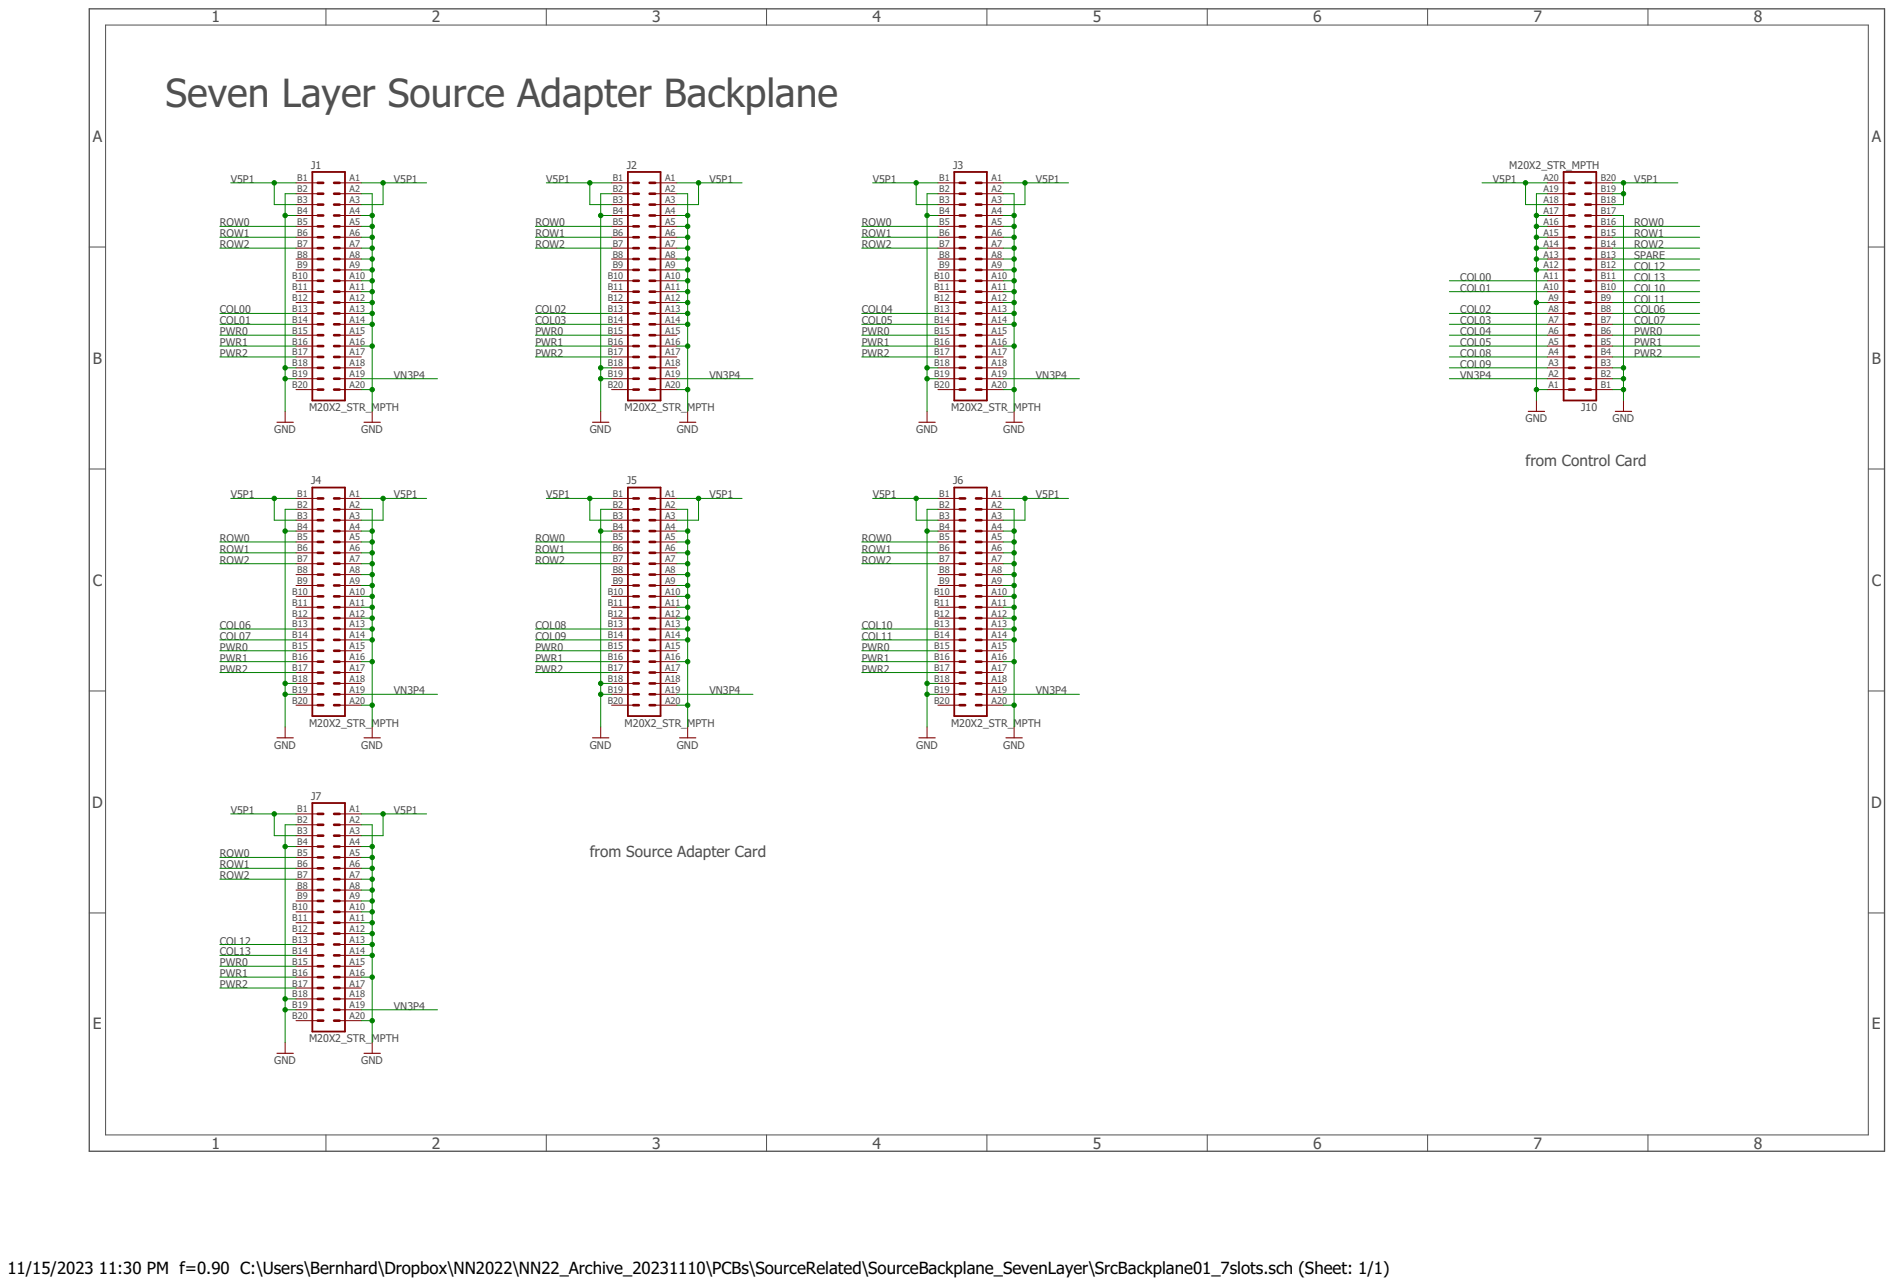
[picture p102: page 1]

Seven Layer Source Adapter Backplane

from Source Adapter Card

11/15/2023 11:30 PM f=0.90 C:\Users\Bernhard\Dropbox\NN2022\NN22_Archive_20231110\PCBs\SourceRelated\SourceBackplane_SevenLayer\SrcBackplane01_7slots.sch (Sheet: 1/1)
