BUNPC/NN22-Technical-Documents/source-splitter.pdf

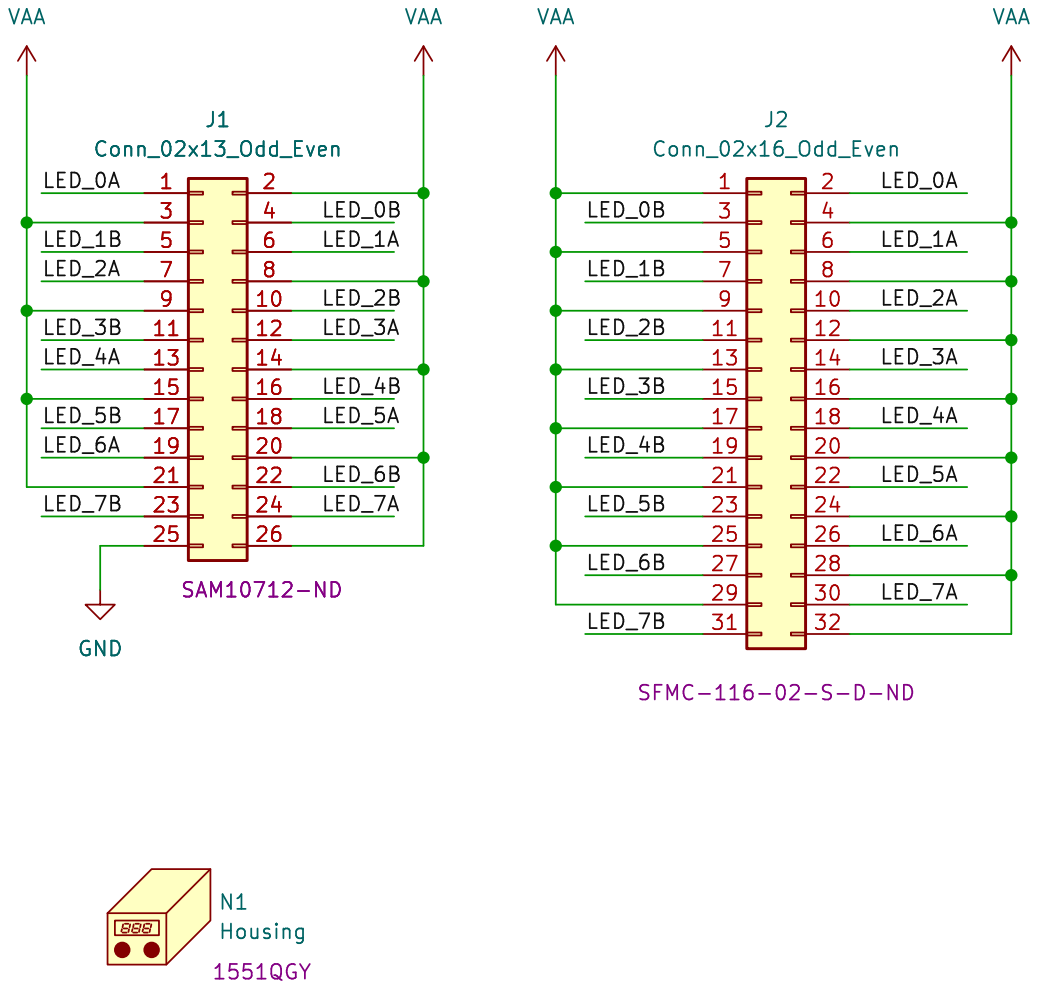
[picture p104: page 1]

Id: 1/1 Title: File: source-splitter.kicad_sch Sheet: / N1 Housing
