BUNPC/NN22-Technical-Documents/Hardware Main/Electronics/Source Electronics/SRC_Backplane/SrcBackplane_SingleLayer/SrcBackplaneSingleLayer00_01.brd

## EAGLE design Hardware Main/Electronics/Source Electronics/SRC_Backplane/SrcBackplane_SingleLayer/SrcBackplaneSingleLayer00_01.brd (2024-05-23)

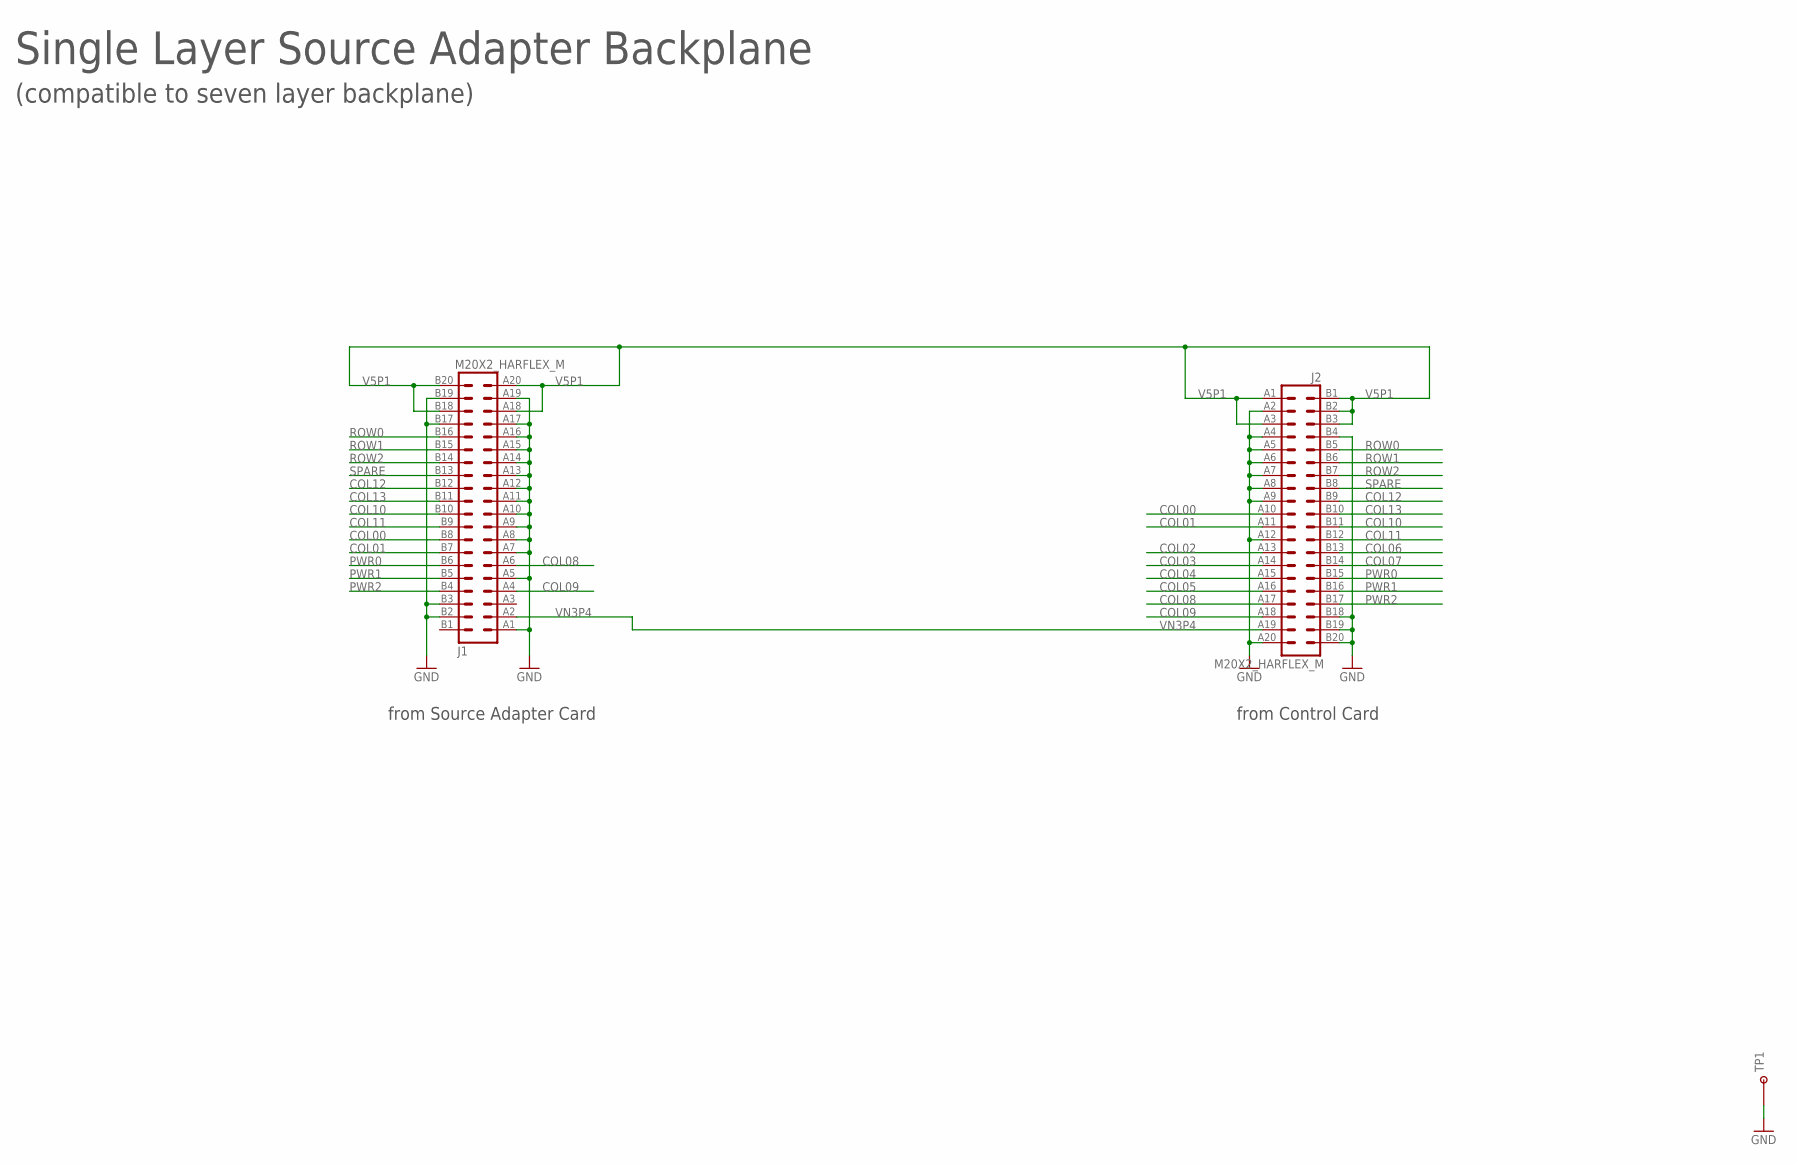
[picture p171: schematic SrcBackplaneSingleLayer00_01.sch]

Parts:
J1, J2: M20X2_HARFLEX_M
TP1: TESTPOINT_ROUND; TESTPAD_ROUND

Connections:
COL00: J1.B8 (15), J2.A10 (20)
COL01: J1.B7 (13), J2.A11 (22)
COL02: J2.A13 (26)
COL03: J2.A14 (28)
COL04: J2.A15 (30)
COL05: J2.A16 (32)
COL06: J2.B13 (25)
COL07: J2.B14 (27)
COL08: J1.A6 (12), J2.A17 (34)
COL09: J1.A4 (8), J2.A18 (36)
COL10: J1.B10 (19), J2.B11 (21)
COL11: J1.B9 (17), J2.B12 (23)
COL12: J1.B12 (23), J2.B9 (17)
COL13: J1.B11 (21), J2.B10 (19)
GND: J1.A1 (2), J1.A5 (10), J1.A7 (14), J1.A8 (16), J1.A9 (18), J1.A10 (20), J1.A11 (22), J1.A12 (24), J1.A13 (26), J1.A14 (28), J1.A15 (30), J1.A16 (32), J1.A17 (34), J1.A19 (38), J1.B2 (3), J1.B3 (5), J1.B17 (33), J1.B19 (37), J2.A2 (4), J2.A4 (8), J2.A5 (10), J2.A6 (12), J2.A7 (14), J2.A8 (16), J2.A9 (18), J2.A12 (24), J2.A20 (40), J2.B4 (7), J2.B18 (35), J2.B19 (37), J2.B20 (39), TP1.P$1
PWR0: J1.B6 (11), J2.B15 (29)
PWR1: J1.B5 (9), J2.B16 (31)
PWR2: J1.B4 (7), J2.B17 (33)
ROW0: J1.B16 (31), J2.B5 (9)
ROW1: J1.B15 (29), J2.B6 (11)
ROW2: J1.B14 (27), J2.B7 (13)
SPARE: J1.B13 (25), J2.B8 (15)
V5P1: J1.A18 (36), J1.A20 (40), J1.B18 (35), J1.B20 (39), J2.A1 (2), J2.A3 (6), J2.B1 (1), J2.B2 (3), J2.B3 (5)
VN3P4: J1.A2 (4), J2.A19 (38)

Notes on the sheet:
Single Layer Source Adapter Backplane
from Source Adapter Card
from Control Card
(compatible to seven layer backplane)

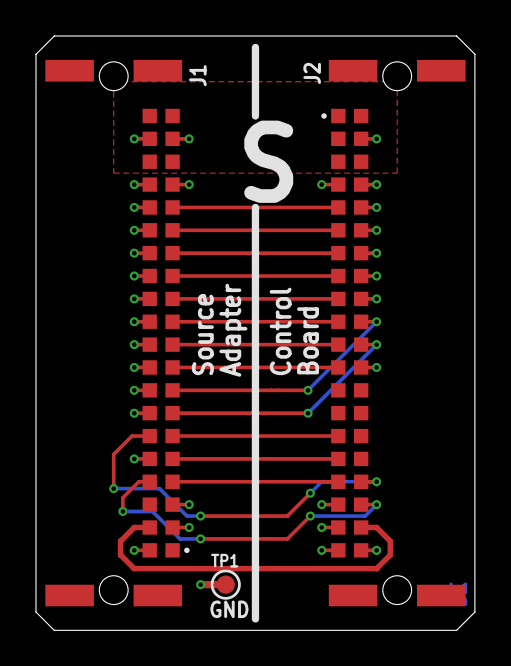
[picture p172: board SrcBackplaneSingleLayer00_01.brd from above]

Board: 2 copper layers, 24.4 x 33.0 mm, 3 parts (0 on the bottom side), 18 nets.
